fernandodaniele/TD3-ProyectoTitulador/Carcasa-Bomba/Modelo.PNG

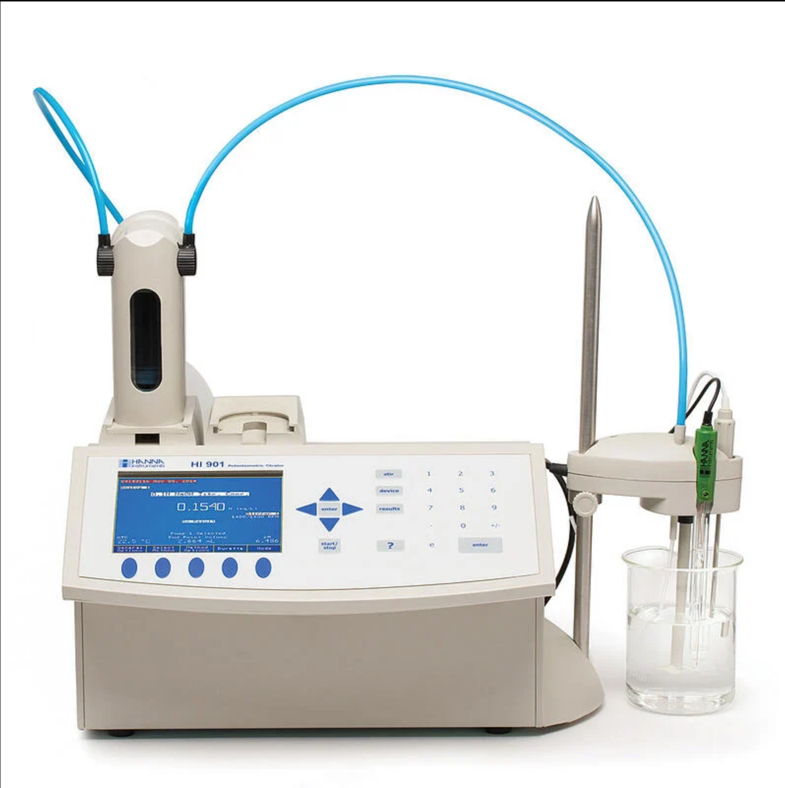
Carcasa-Bomba/Modelo.PNG
