fernandodaniele/TD3-ProyectoTitulador/Carcasa-Bomba/Agujas.PNG

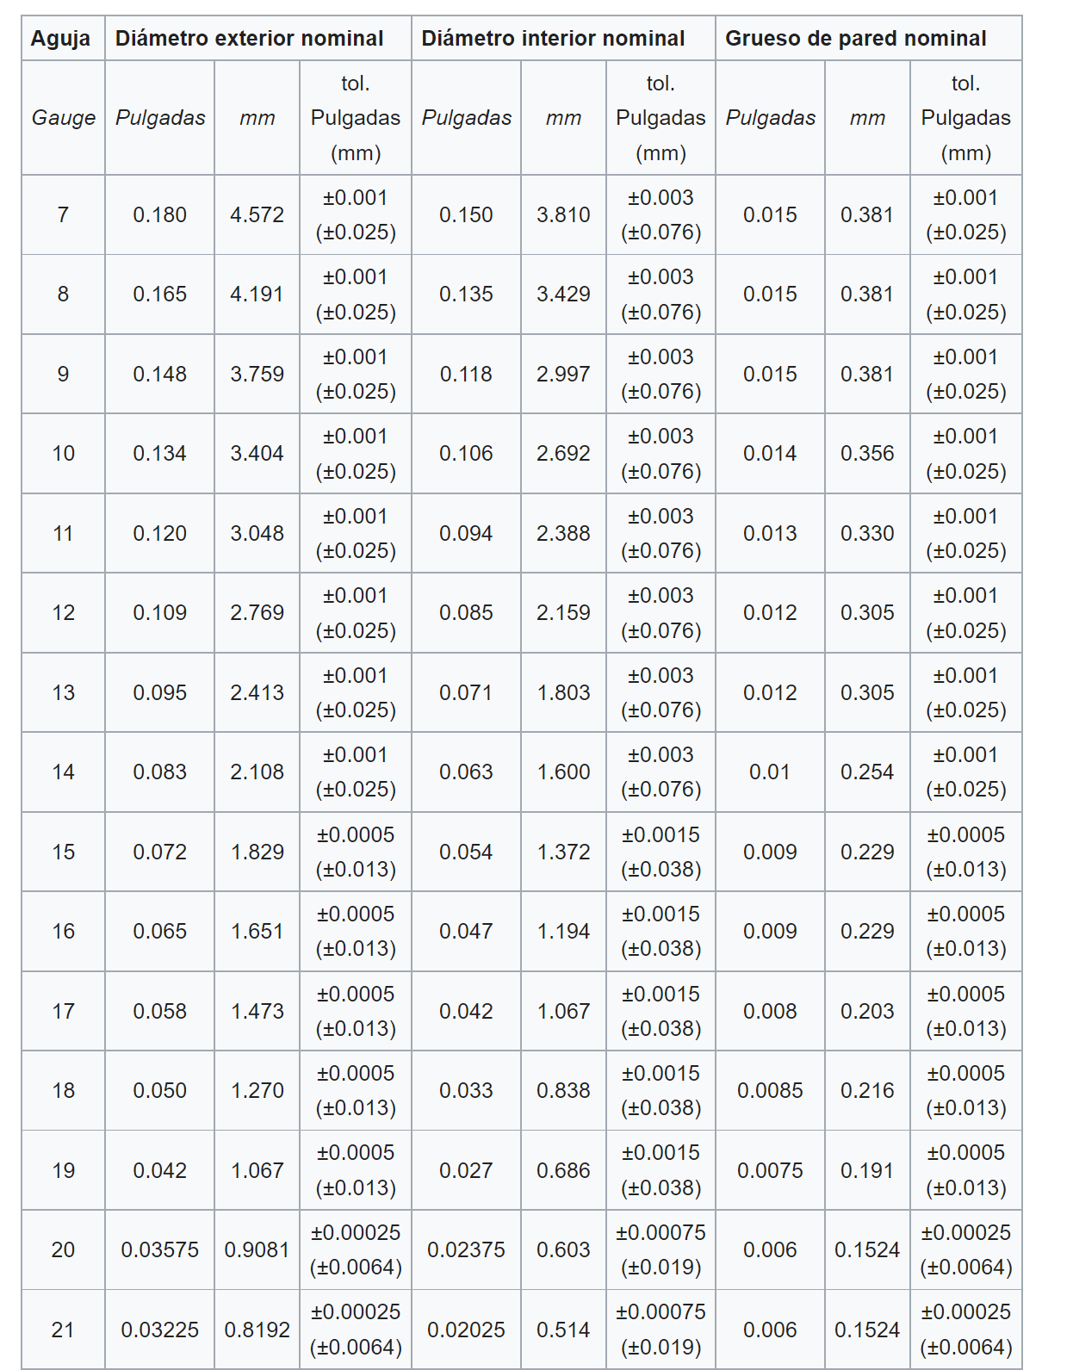
Carcasa-Bomba/Agujas.PNG
