fernandodaniele/TD3-ProyectoTitulador/Carcasa-Bomba/Captura.PNG

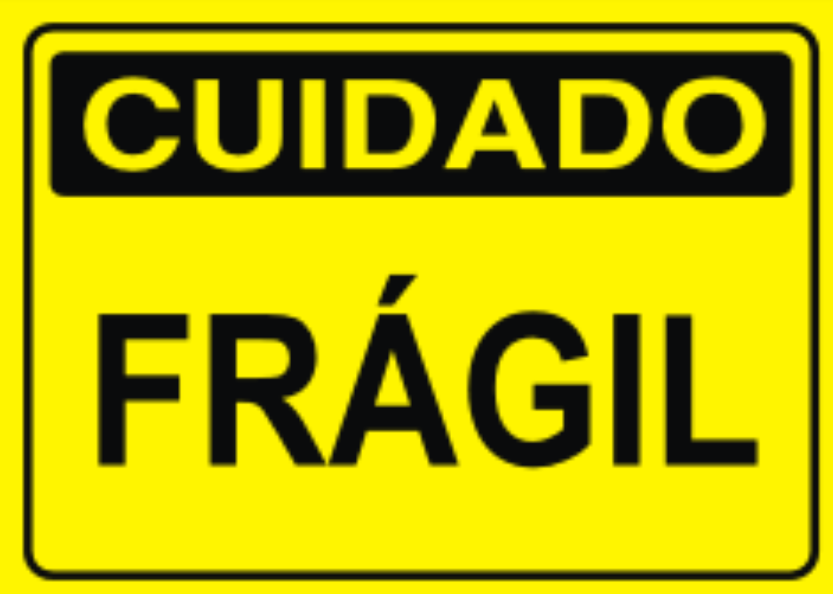
Carcasa-Bomba/Captura.PNG
