fernandodaniele/TD3-ProyectoTitulador/Holas de datos y especificaciones/Datos motor, bomba y driver/page2.png

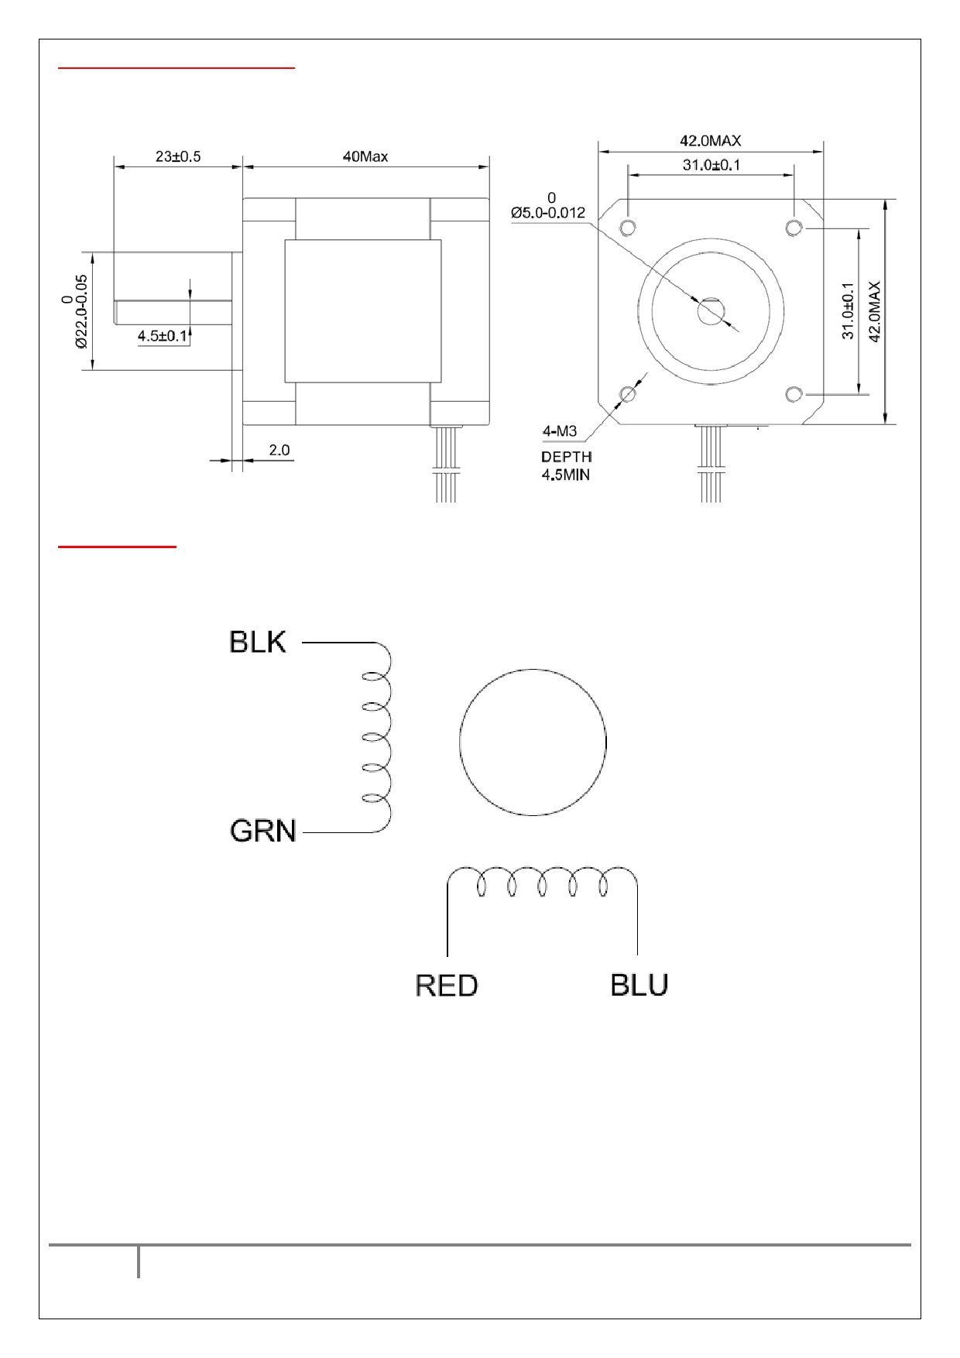
Holas de datos y especificaciones/Datos motor, bomba y driver/page2.png
