fernandodaniele/TD3-ProyectoTitulador/Holas de datos y especificaciones/Display MCUFRIEND2.jpeg

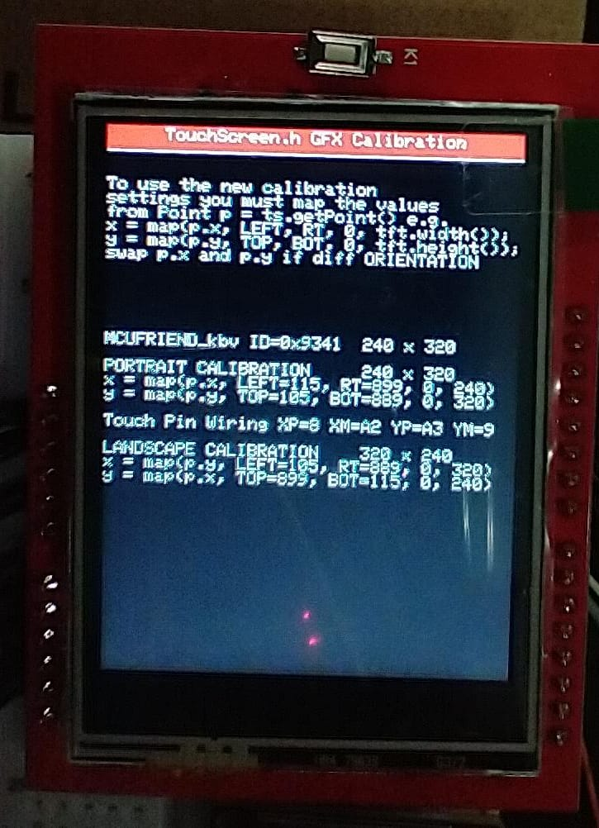
Holas de datos y especificaciones/Display MCUFRIEND2.jpeg
