fernandodaniele/TD3-ProyectoTitulador/Holas de datos y especificaciones/Display MCUFRIEND.jpeg

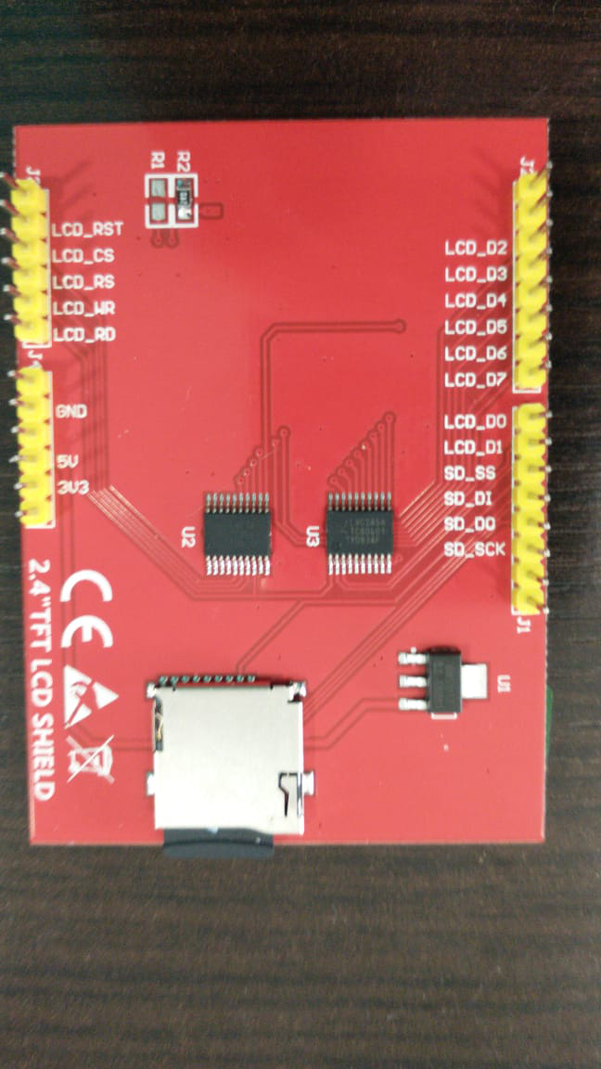
Holas de datos y especificaciones/Display MCUFRIEND.jpeg
