fernandodaniele/TD3-ProyectoTitulador/Holas de datos y especificaciones/MEF menu titulador.jpg

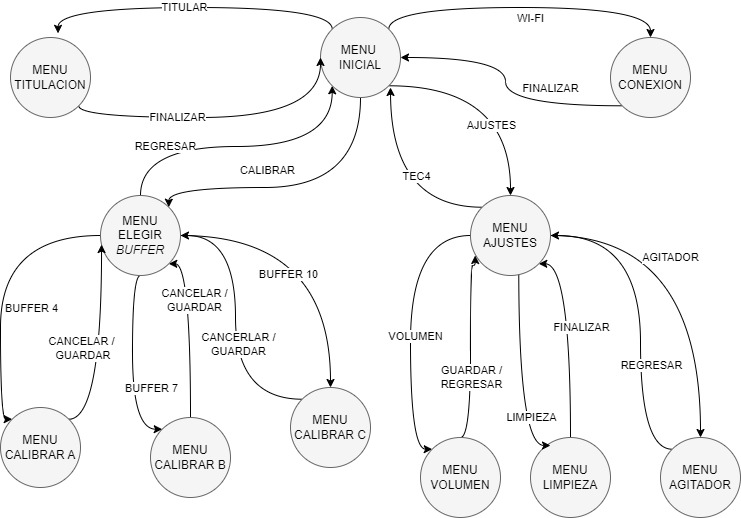
Holas de datos y especificaciones/MEF menu titulador.jpg
