fernandodaniele/TD3-ProyectoTitulador/Carcasa-Bomba/BATIDOR.SLDPRT

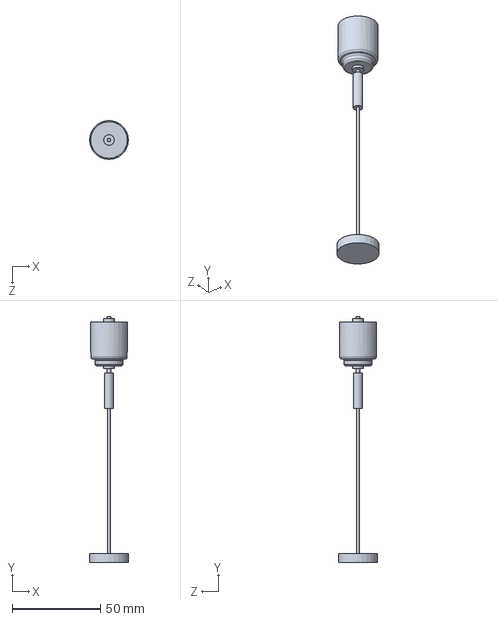
[picture p26: CAD file, 2024-11-25]
Carcasa-Bomba/BATIDOR.SLDPRT
22.0 x 139.0 x 22.0 mm
