fernandodaniele/TD3-ProyectoTitulador/Carcasa-Bomba/Peristaltic Pump 2020/rodillos.SLDPRT

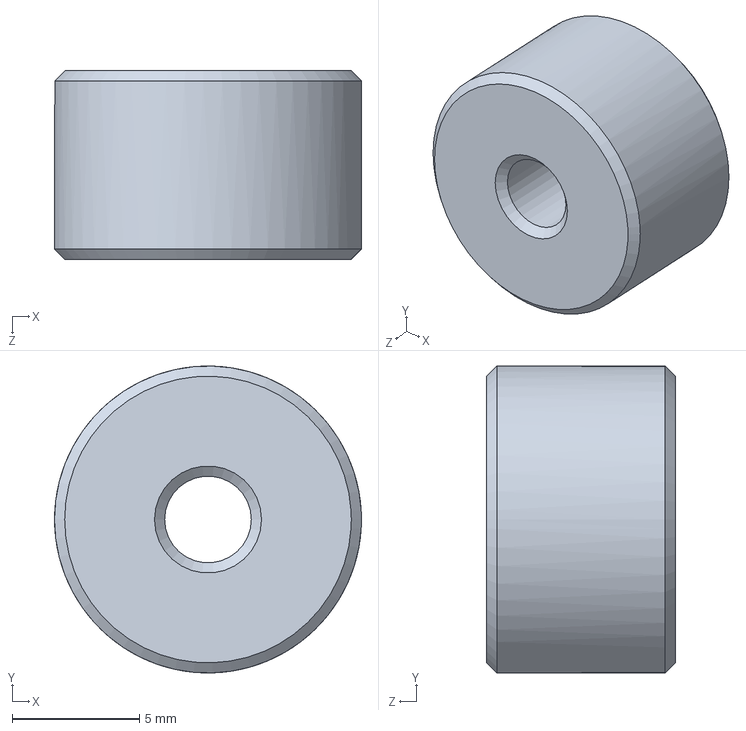
[picture p27: CAD file, 2024-11-25]
Carcasa-Bomba/Peristaltic Pump 2020/rodillos.SLDPRT
12.1 x 12.0 x 7.40 mm
