fernandodaniele/TD3-ProyectoTitulador/Carcasa-Bomba/Peristaltic Pump 2020/apoyo.SLDPRT

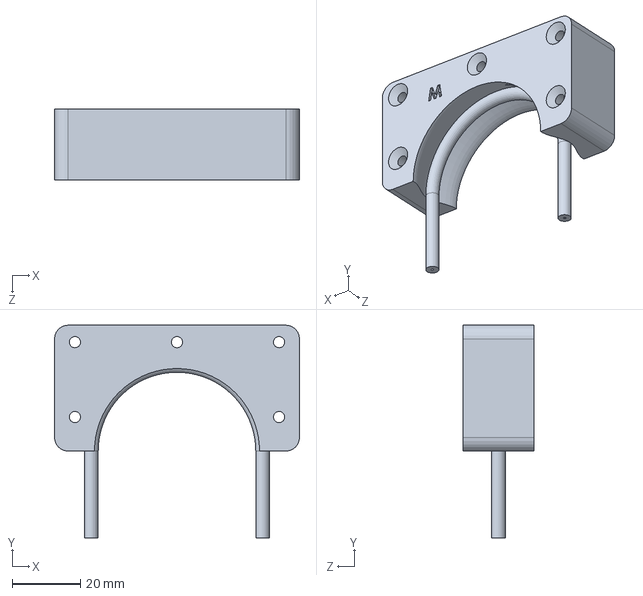
[picture p28: CAD file, 2024-11-25]
Carcasa-Bomba/Peristaltic Pump 2020/apoyo.SLDPRT
72.0 x 62.5 x 21.0 mm
