fernandodaniele/TD3-ProyectoTitulador/Carcasa-Bomba/Peristaltic Pump 2020/STL/bomba - clamp-2.STL

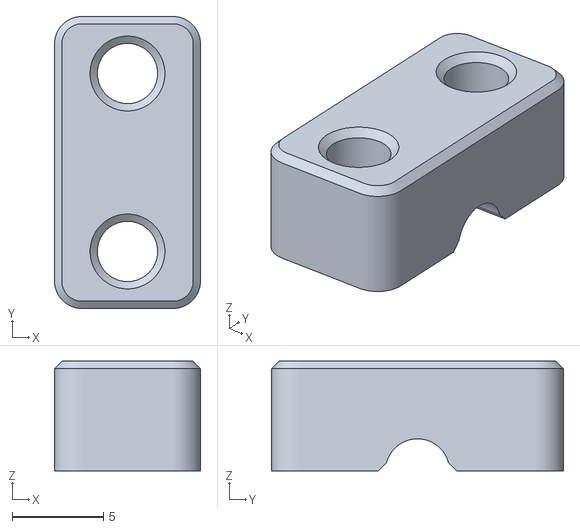
[picture p29: CAD file, 2024-11-25]
Carcasa-Bomba/Peristaltic Pump 2020/STL/bomba - clamp-2.STL
8.00 x 16.0 x 6.00
