fernandodaniele/TD3-ProyectoTitulador/Carcasa-Bomba/Plaqueta.SLDPRT

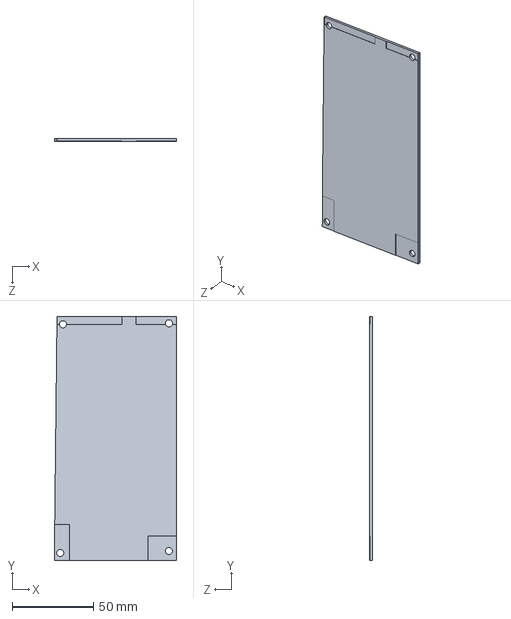
[picture p30: CAD file, 2024-11-25]
Carcasa-Bomba/Plaqueta.SLDPRT
75.2 x 150.0 x 1.75 mm
