fernandodaniele/TD3-ProyectoTitulador/Carcasa-Bomba/Carcasa tapa.SLDPRT

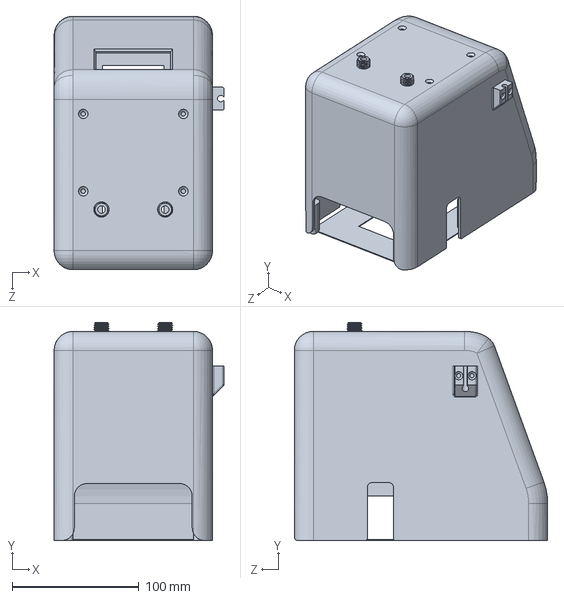
[picture p31: CAD file, 2024-11-25]
Carcasa-Bomba/Carcasa tapa.SLDPRT
134.0 x 172.0 x 200.0 mm
