fernandodaniele/TD3-ProyectoTitulador/Carcasa-Bomba/Peristaltic Pump 2020/Tornillo}.SLDPRT

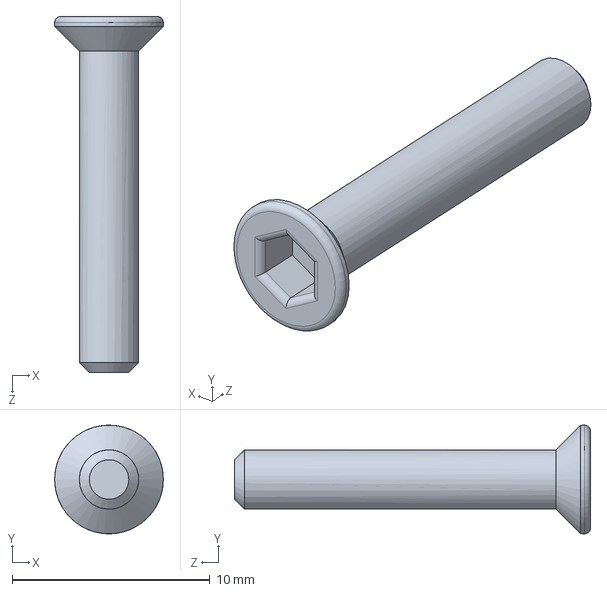
[picture p32: CAD file, 2024-11-25]
Carcasa-Bomba/Peristaltic Pump 2020/Tornillo}.SLDPRT
5.50 x 5.50 x 18.0 mm
