fernandodaniele/TD3-ProyectoTitulador/Carcasa-Bomba/Buje.3MF

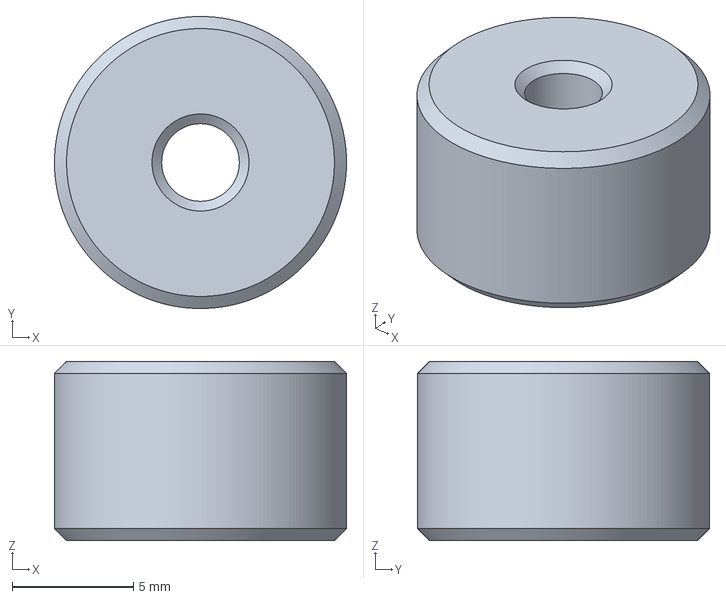
[picture p33: CAD file, 2024-11-25]
Carcasa-Bomba/Buje.3MF
12.1 x 12.0 x 7.40 mm
