fernandodaniele/TD3-ProyectoTitulador/Carcasa-Bomba/Peristaltic Pump 2020/Plato cabezal eje.SLDPRT

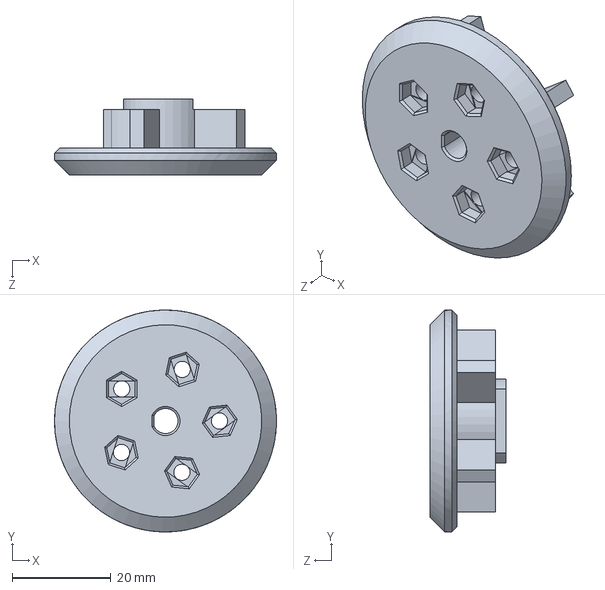
[picture p34: CAD file, 2024-11-25]
Carcasa-Bomba/Peristaltic Pump 2020/Plato cabezal eje.SLDPRT
45.0 x 45.0 x 15.5 mm
