fernandodaniele/TD3-ProyectoTitulador/Carcasa-Bomba/Peristaltic Pump 2020/Manguera flexible.SLDPRT

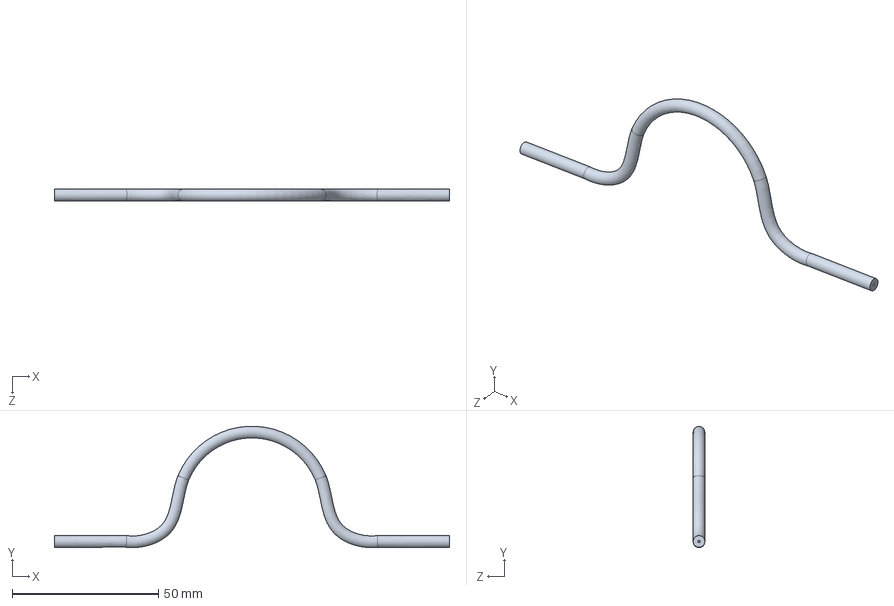
[picture p35: CAD file, 2024-11-25]
Carcasa-Bomba/Peristaltic Pump 2020/Manguera flexible.SLDPRT
135.2 x 41.5 x 4.00 mm
