fernandodaniele/TD3-ProyectoTitulador/Carcasa-Bomba/Plato cabezal eje.3MF

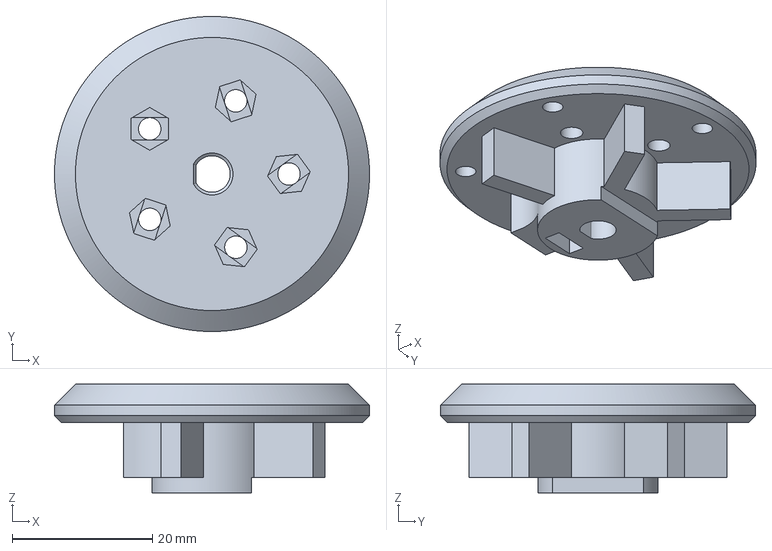
[picture p36: CAD file, 2024-11-25]
Carcasa-Bomba/Plato cabezal eje.3MF
45.0 x 45.0 x 15.5 mm
