fernandodaniele/TD3-ProyectoTitulador/Carcasa-Bomba/Peristaltic Pump 2020/Perno Precision.SLDPRT

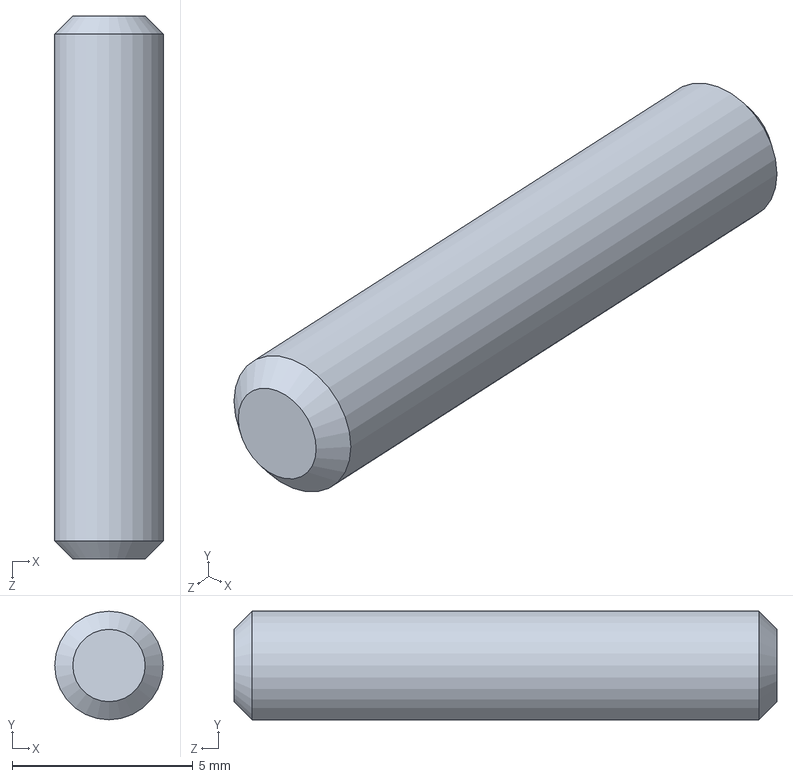
[picture p37: CAD file, 2024-11-25]
Carcasa-Bomba/Peristaltic Pump 2020/Perno Precision.SLDPRT
3.00 x 3.00 x 15.0 mm
