fernandodaniele/TD3-ProyectoTitulador/Carcasa-Bomba/Tapa cabezal.SLDPRT

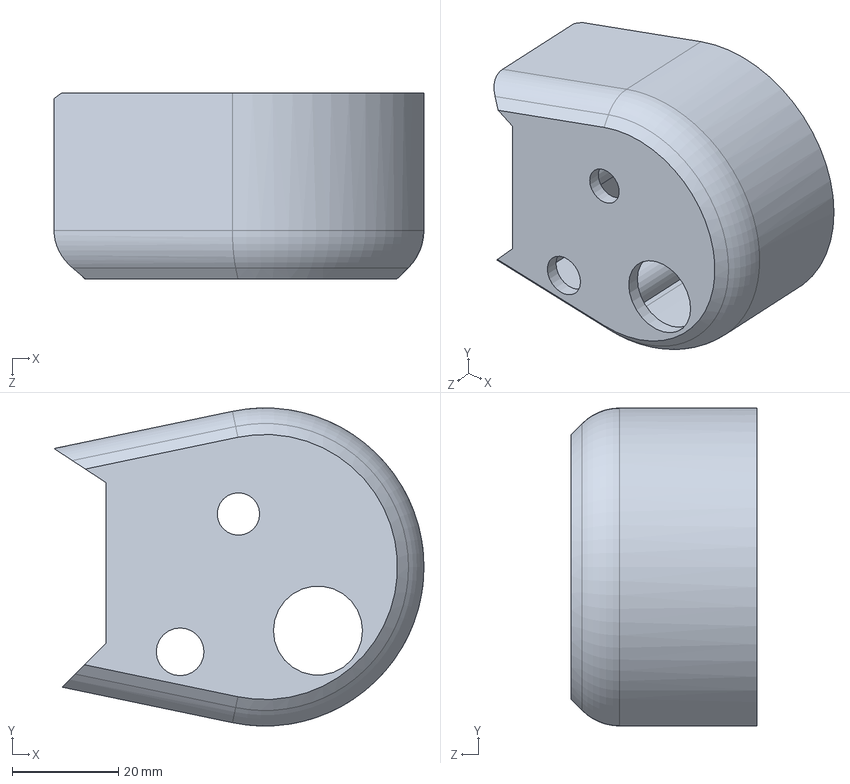
[picture p38: CAD file, 2024-11-25]
Carcasa-Bomba/Tapa cabezal.SLDPRT
69.8 x 60.0 x 35.0 mm
