fernandodaniele/TD3-ProyectoTitulador/Carcasa-Bomba/Peristaltic Pump 2020/base.SLDPRT

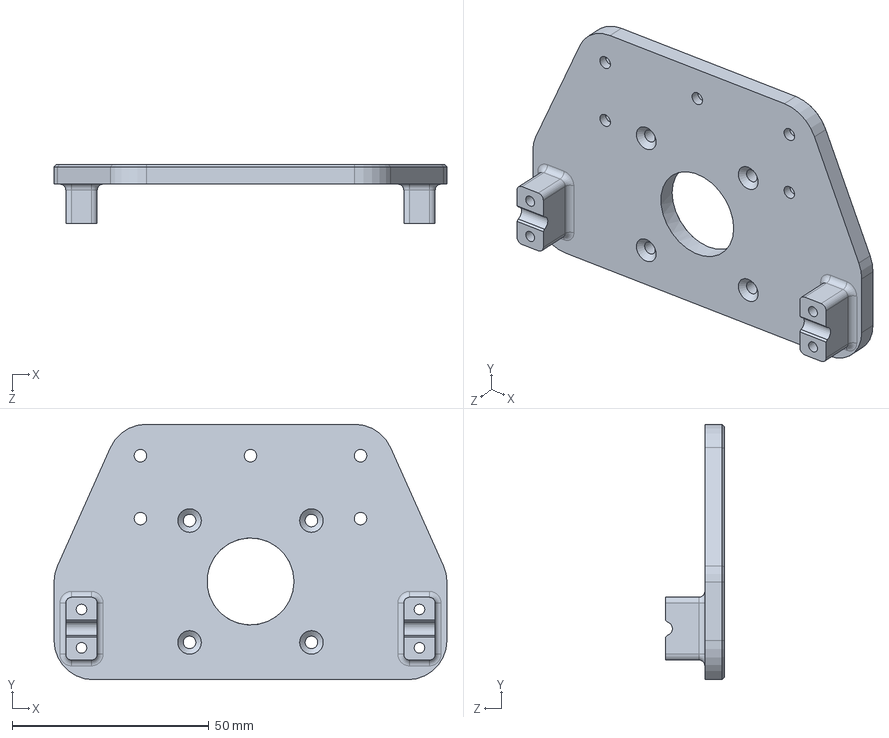
[picture p39: CAD file, 2024-11-25]
Carcasa-Bomba/Peristaltic Pump 2020/base.SLDPRT
100.0 x 65.0 x 15.0 mm
