fernandodaniele/TD3-ProyectoTitulador/Carcasa-Bomba/Tornillo apriete.SLDPRT

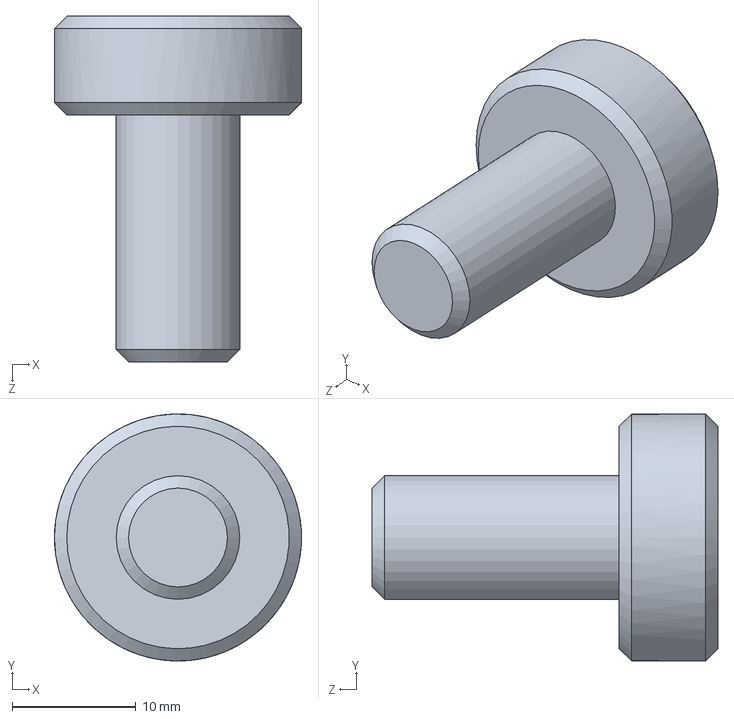
[picture p40: CAD file, 2024-11-25]
Carcasa-Bomba/Tornillo apriete.SLDPRT
20.0 x 20.0 x 28.0 mm
