fernandodaniele/TD3-ProyectoTitulador/Carcasa-Bomba/Logo_SensorPH.SLDPRT

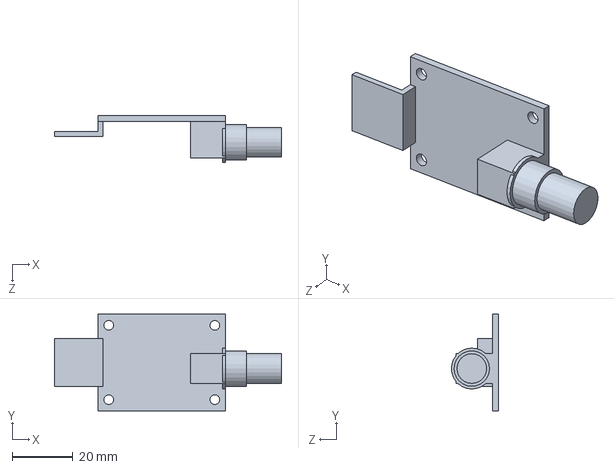
[picture p41: CAD file, 2024-11-25]
Carcasa-Bomba/Logo_SensorPH.SLDPRT
74.9 x 32.0 x 15.6 mm
