fernandodaniele/TD3-ProyectoTitulador/Carcasa-Bomba/Racor 3d.SLDPRT

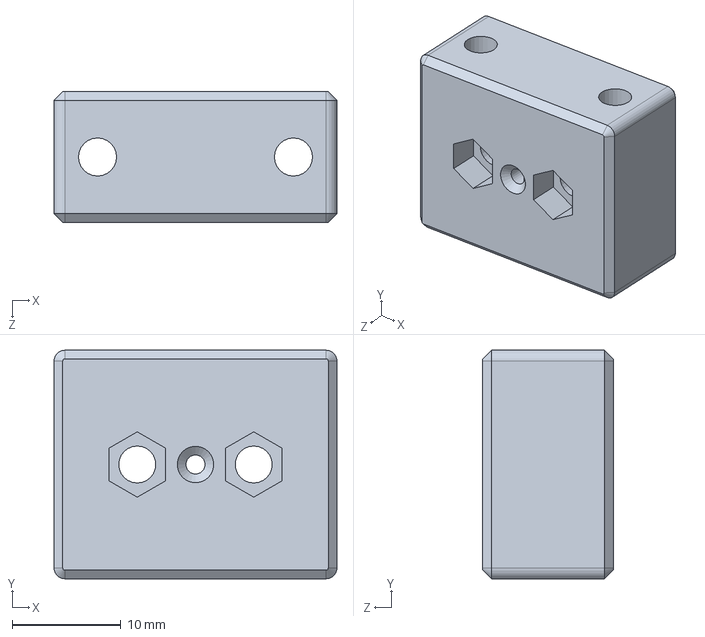
[picture p42: CAD file, 2024-11-25]
Carcasa-Bomba/Racor 3d.SLDPRT
26.0 x 21.0 x 12.0 mm
