fernandodaniele/TD3-ProyectoTitulador/Carcasa-Bomba/agarre racor mangueras.SLDPRT

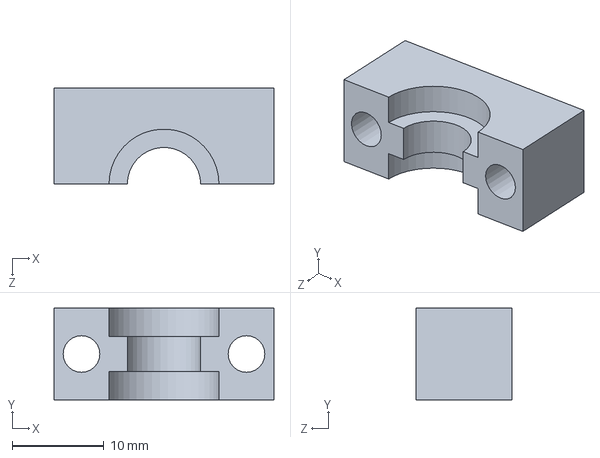
[picture p43: CAD file, 2024-11-25]
Carcasa-Bomba/agarre racor mangueras.SLDPRT
24.0 x 10.0 x 10.5 mm
