fernandodaniele/TD3-ProyectoTitulador/Carcasa-Bomba/TAPONES.SLDPRT

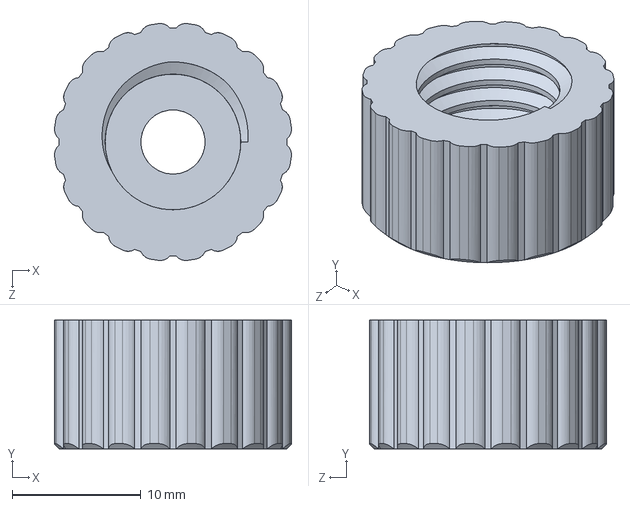
[picture p44: CAD file, 2024-11-25]
Carcasa-Bomba/TAPONES.SLDPRT
18.4 x 10.0 x 18.4 mm
