fernandodaniele/TD3-ProyectoTitulador/Carcasa-Bomba/Tornillo Fix 3 x XX.SLDPRT

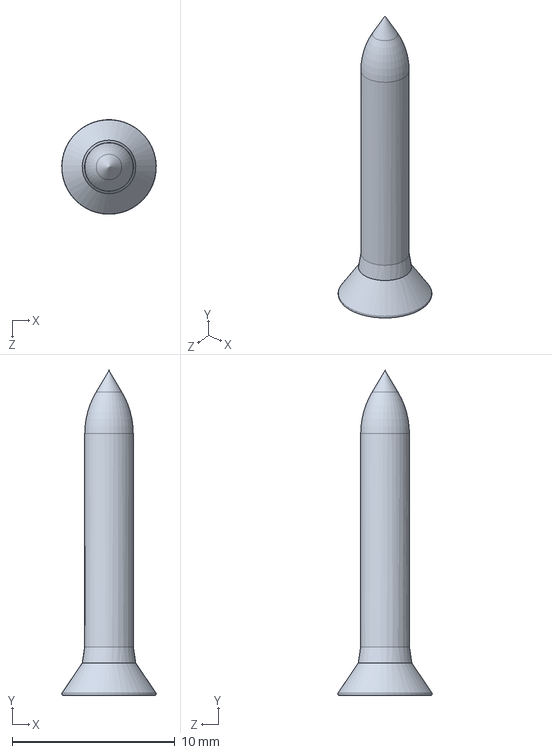
[picture p45: CAD file, 2024-11-25]
Carcasa-Bomba/Tornillo Fix 3 x XX.SLDPRT
5.82 x 20.0 x 5.82 mm
