fernandodaniele/TD3-ProyectoTitulador/Carcasa-Bomba/Switch on-ff.SLDPRT

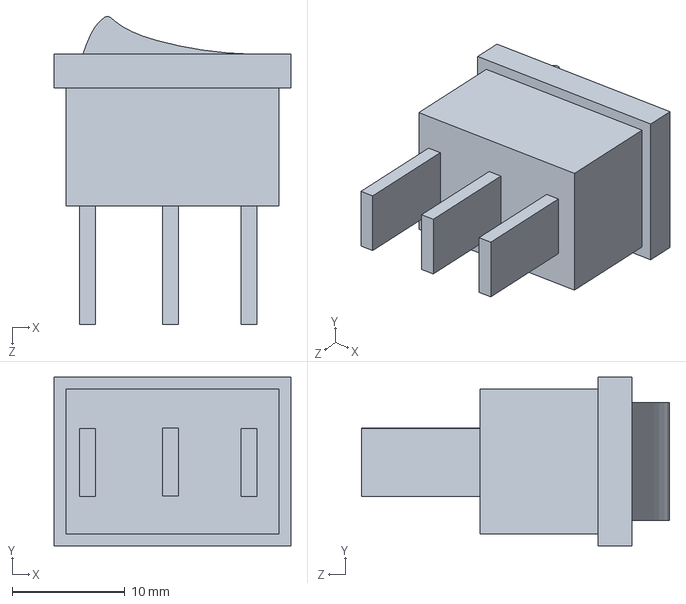
[picture p46: CAD file, 2024-11-25]
Carcasa-Bomba/Switch on-ff.SLDPRT
21.0 x 15.0 x 27.3 mm
