fernandodaniele/TD3-ProyectoTitulador/Carcasa-Bomba/Barra 12.SLDPRT

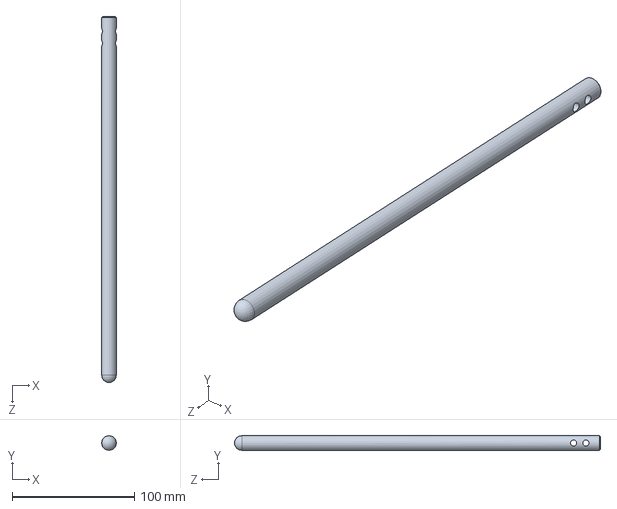
[picture p47: CAD file, 2024-11-25]
Carcasa-Bomba/Barra 12.SLDPRT
12.0 x 12.0 x 300.0 mm
