fernandodaniele/TD3-ProyectoTitulador/Carcasa-Bomba/electrodo.SLDPRT

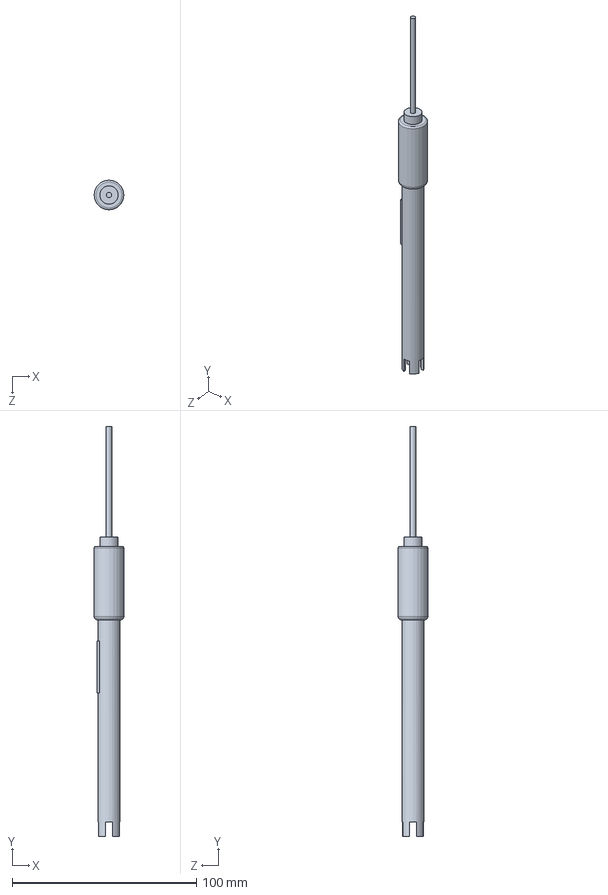
[picture p48: CAD file, 2024-11-25]
Carcasa-Bomba/electrodo.SLDPRT
16.1 x 222.5 x 16.1 mm
