fernandodaniele/TD3-ProyectoTitulador/Carcasa-Bomba/Basetitulador.SLDPRT

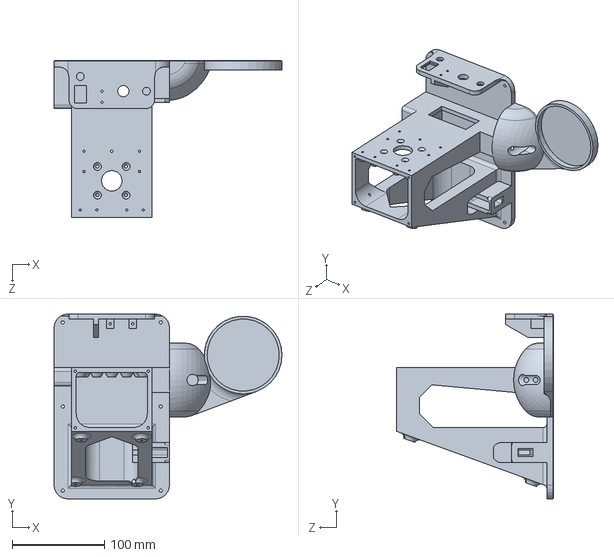
[picture p49: CAD file, 2024-11-25]
Carcasa-Bomba/Basetitulador.SLDPRT
246.7 x 200.0 x 169.5 mm
