fernandodaniele/TD3-ProyectoTitulador/Carcasa-Bomba/Cabezal.SLDPRT

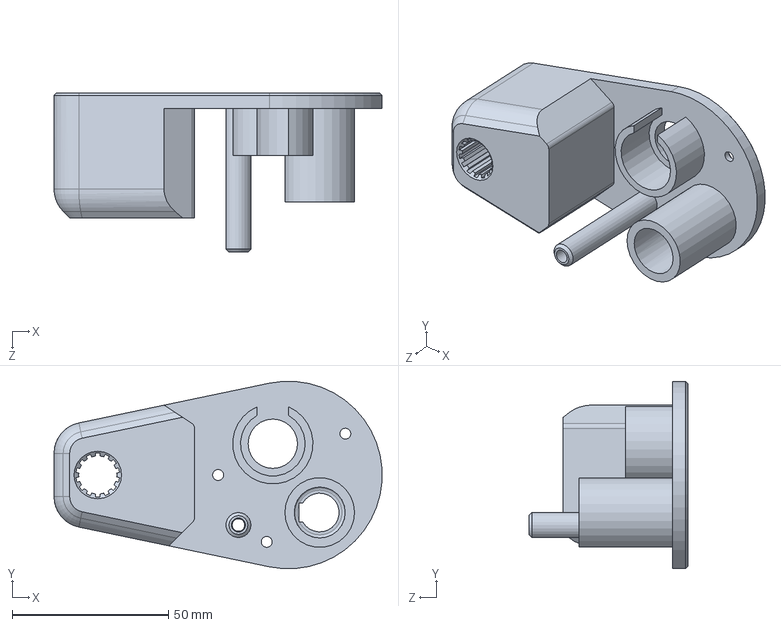
[picture p50: CAD file, 2024-11-25]
Carcasa-Bomba/Cabezal.SLDPRT
104.9 x 59.9 x 51.0 mm
