fernandodaniele/TD3-ProyectoTitulador/Carcasa-Bomba/Soporte Probetas.SLDPRT

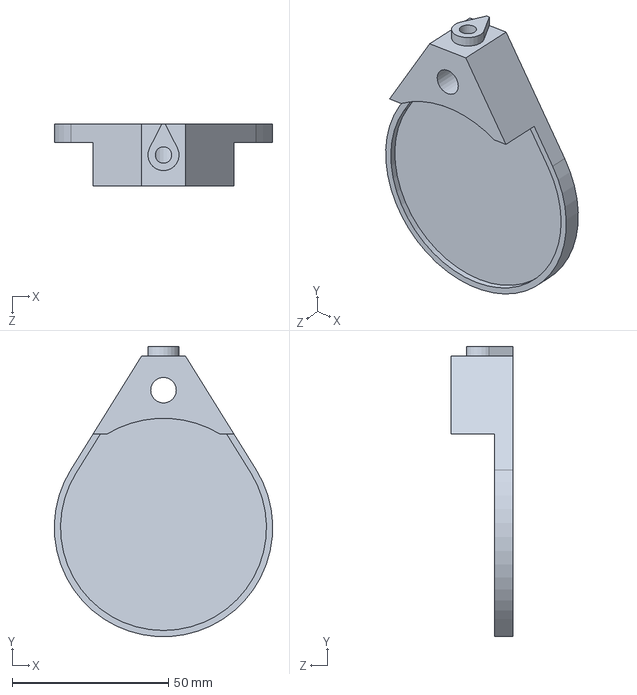
[picture p51: CAD file, 2024-11-25]
Carcasa-Bomba/Soporte Probetas.SLDPRT
69.9 x 92.9 x 20.0 mm
