fernandodaniele/TD3-ProyectoTitulador/Carcasa-Bomba/Porta vaso.SLDPRT

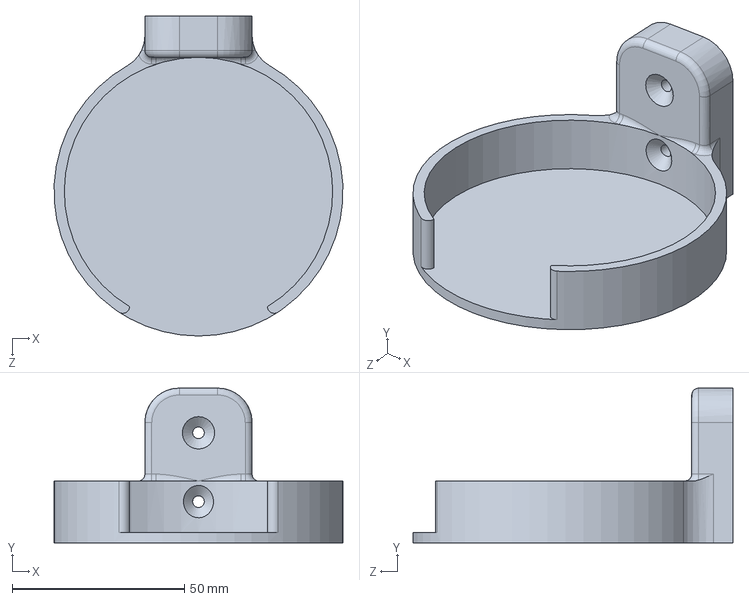
[picture p52: CAD file, 2024-11-25]
Carcasa-Bomba/Porta vaso.SLDPRT
83.9 x 45.0 x 93.0 mm
