fernandodaniele/TD3-ProyectoTitulador/Carcasa-Bomba/Conector potencia y motor.SLDPRT

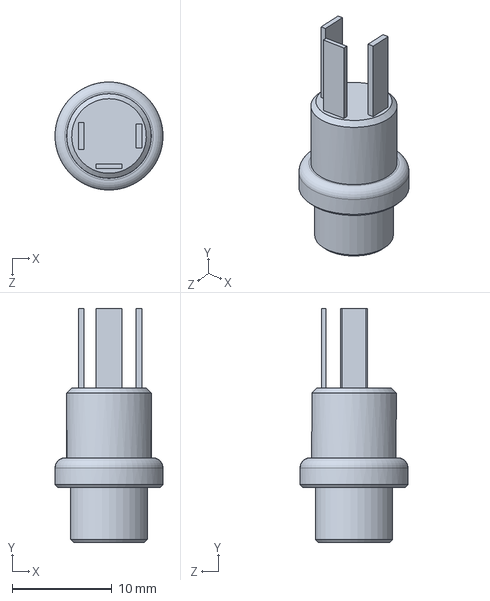
[picture p53: CAD file, 2024-11-25]
Carcasa-Bomba/Conector potencia y motor.SLDPRT
10.9 x 23.5 x 10.9 mm
