fernandodaniele/TD3-ProyectoTitulador/Carcasa-Bomba/Soporte Lapiz.3MF

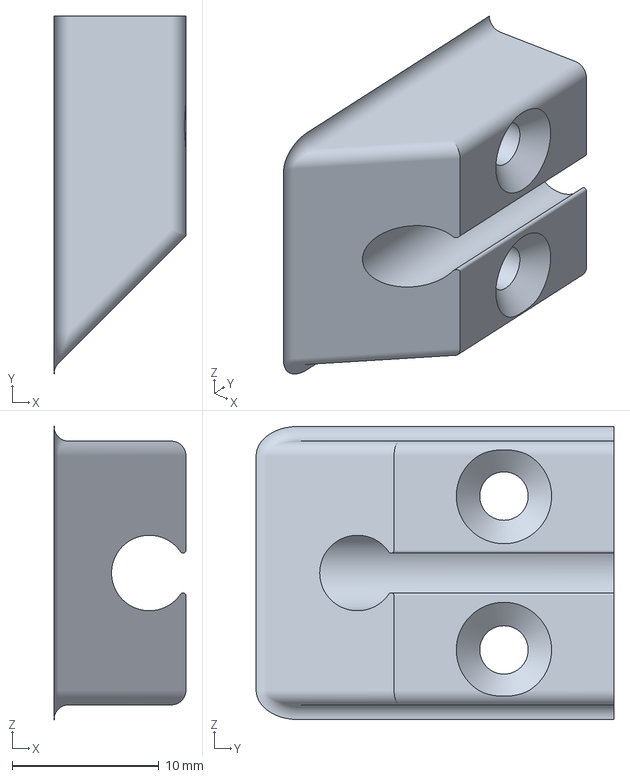
[picture p54: CAD file, 2024-11-25]
Carcasa-Bomba/Soporte Lapiz.3MF
9.00 x 24.4 x 20.0 mm
