fernandodaniele/TD3-ProyectoTitulador/Carcasa-Bomba/racor mangueras.SLDPRT

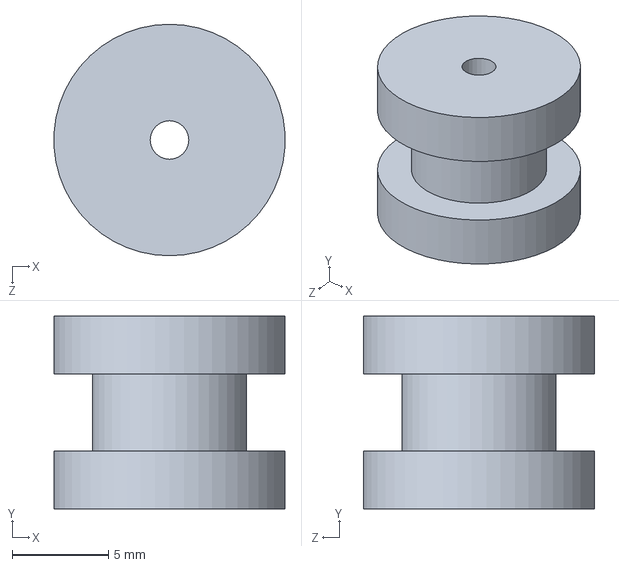
[picture p55: CAD file, 2024-11-25]
Carcasa-Bomba/racor mangueras.SLDPRT
12.0 x 10.0 x 12.0 mm
