fernandodaniele/TD3-ProyectoTitulador/Carcasa-Bomba/apoyo.3MF

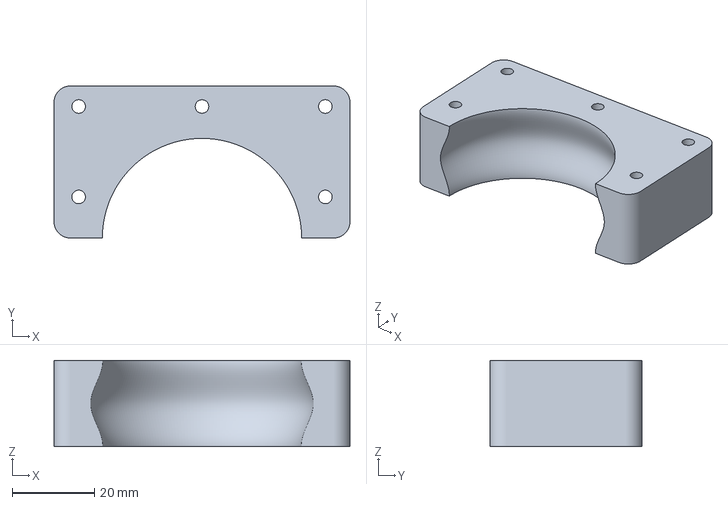
[picture p56: CAD file, 2024-11-25]
Carcasa-Bomba/apoyo.3MF
72.0 x 37.0 x 21.0 mm
