fernandodaniele/TD3-ProyectoTitulador/Carcasa-Bomba/usb.SLDPRT

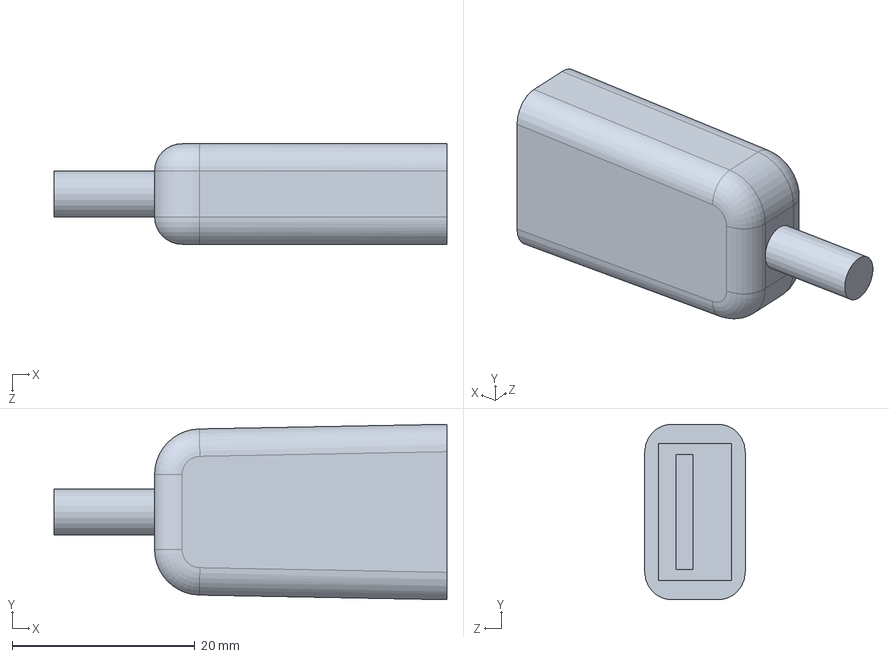
[picture p57: CAD file, 2024-11-25]
Carcasa-Bomba/usb.SLDPRT
43.0 x 19.2 x 11.0 mm
