fernandodaniele/TD3-ProyectoTitulador/Carcasa-Bomba/vaso precipitado.SLDPRT

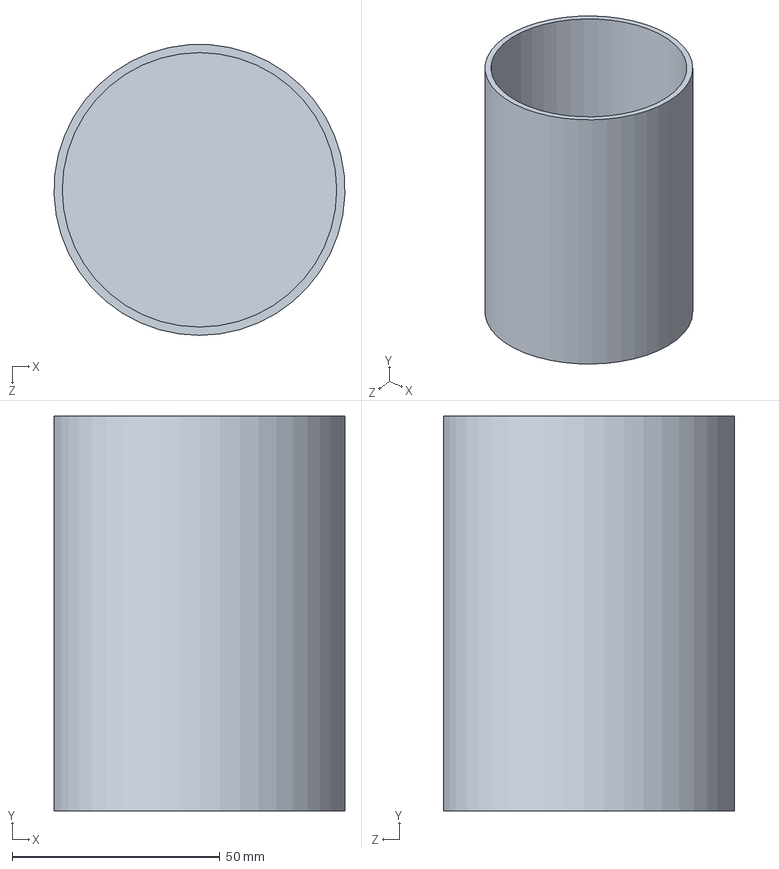
[picture p58: CAD file, 2024-11-25]
Carcasa-Bomba/vaso precipitado.SLDPRT
70.0 x 95.0 x 69.9 mm
