fernandodaniele/TD3-ProyectoTitulador/Programa_Titulador/include/wifi.h

#ifndef WIFI_H
#define WIFI_H

/*==================[Inclusiones]============================================*/

#include "freertos/FreeRTOS.h"
#include "freertos/task.h"
#include "driver/gpio.h"
#include "freertos/semphr.h"
#include "driver/uart.h"
#include "esp_wifi.h"
#include "esp_event.h"
#include "esp_http_server.h"
#include "esp_netif.h"
#include "lwip/ip_addr.h"

/*==================[Definiciones]===================================*/

// #define WIFI_SSID   "."
// #define WIFI_PASS   "43364336"

#define WIFI_SSID "ESP32_AP"   // Nombre de la red WiFi (SSID)
#define WIFI_PASS "12345678"   // Contraseña de la red WiFi (mínimo 8 caracteres)

/*==================[Prototipos de funciones]======================*/

// void wifi_init();
void wifi_init_softap();
httpd_handle_t start_webserver();

#endif
